BDawk/FlightImpact/hardware/enclosure/preview/lid_default.png

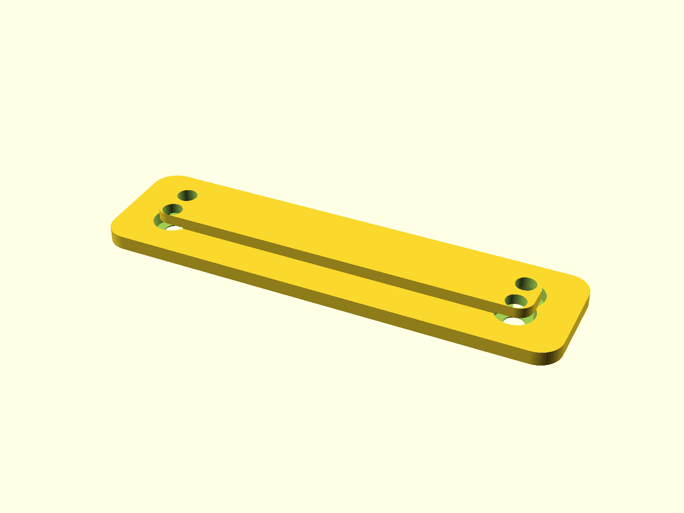
hardware/enclosure/preview/lid_default.png
